joebmz98/MC8P-Mini-MIDI-Controller/images/photos/20260501_085314.jpg

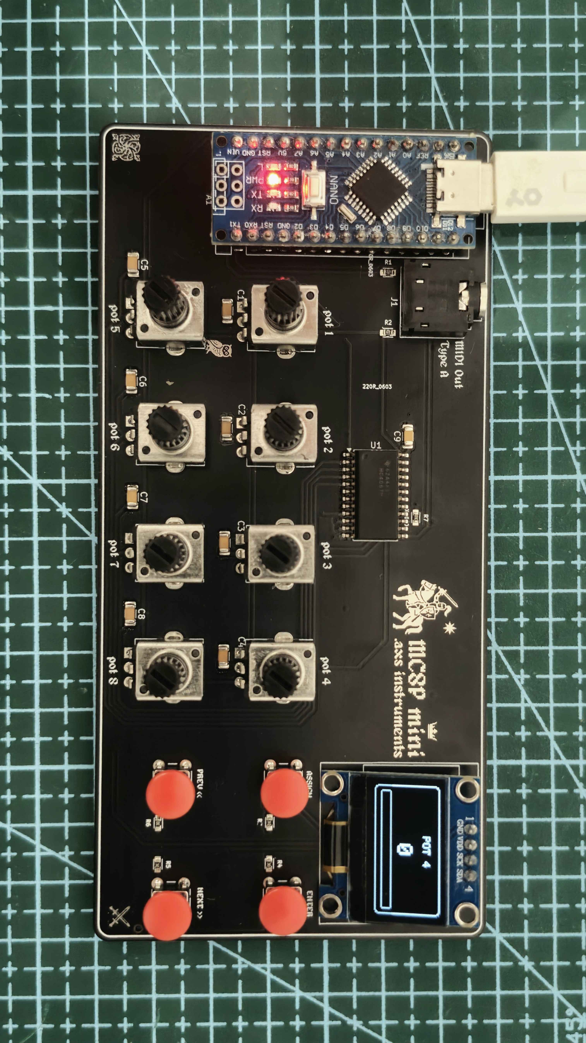
images/photos/20260501_085314.jpg
