joebmz98/MC8P-Mini-MIDI-Controller/images/photos/P1155457.jpg

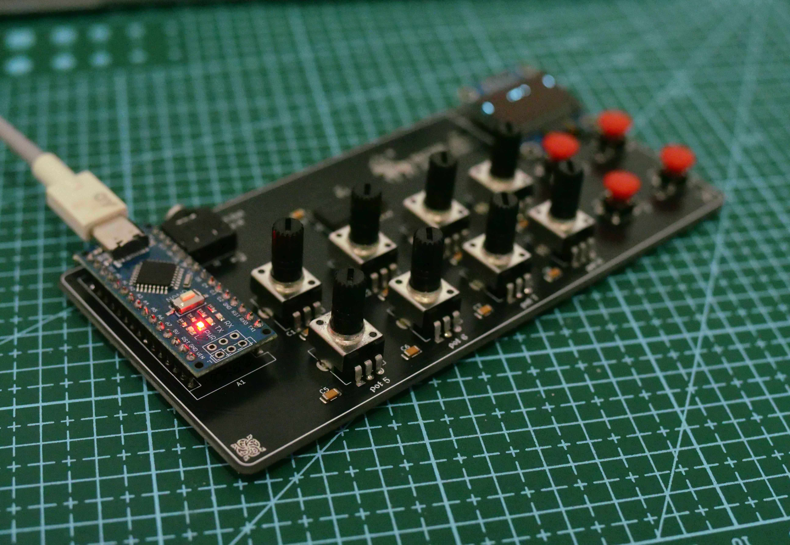
images/photos/P1155457.jpg
