joebmz98/MC8P-Mini-MIDI-Controller/images/photos/P1155459.jpg

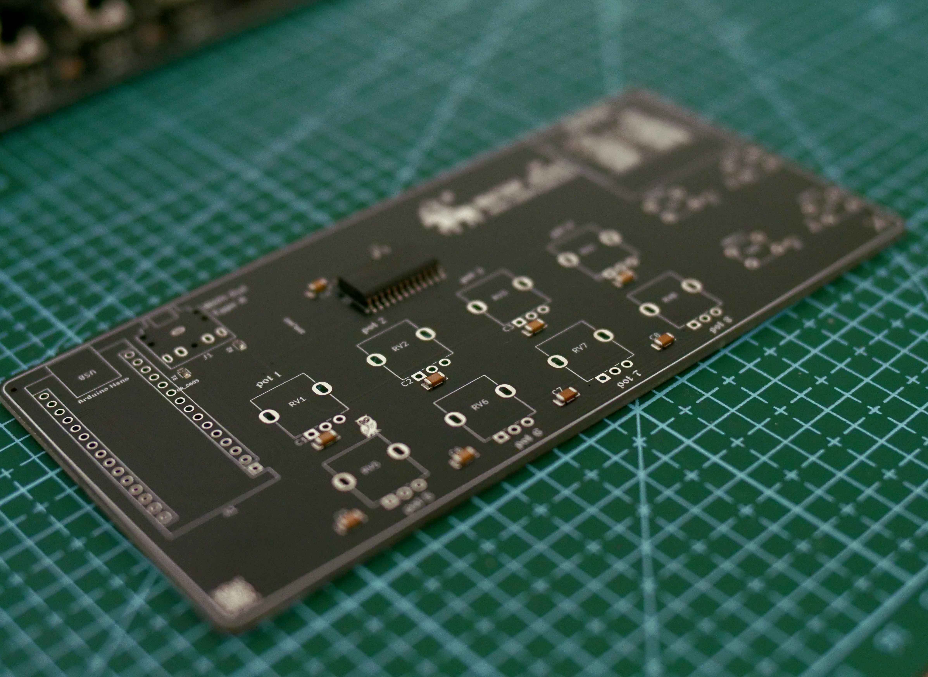
images/photos/P1155459.jpg
