joebmz98/MC8P-Mini-MIDI-Controller/images/photos/P1155460.jpg

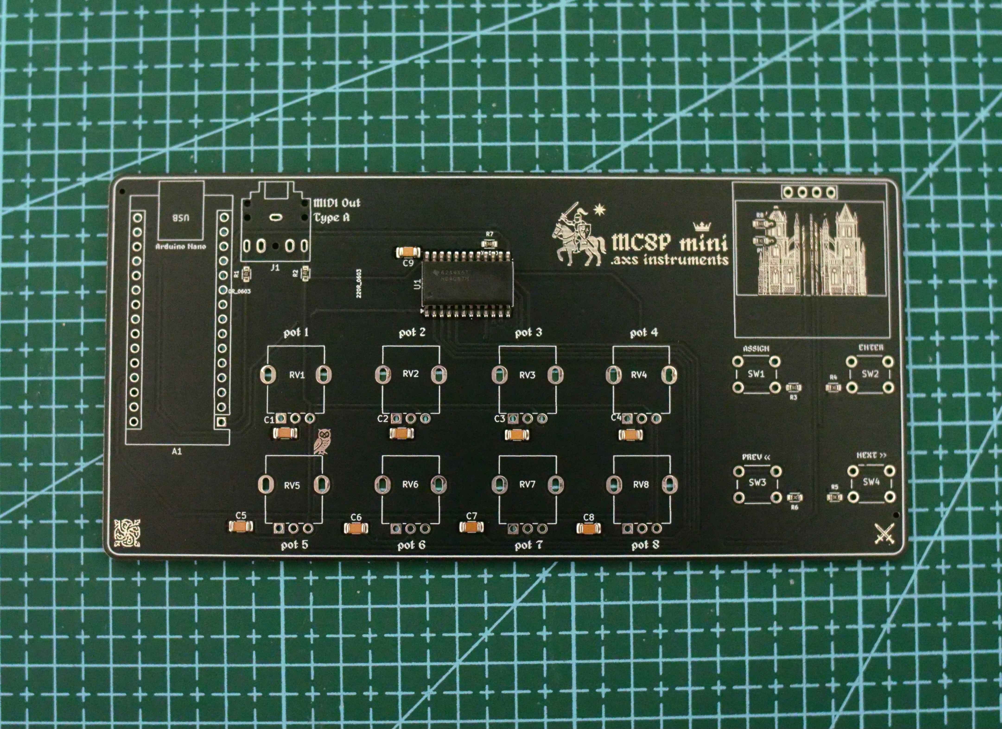
images/photos/P1155460.jpg
