joebmz98/MC8P-Mini-MIDI-Controller/images/photos/P1155462.jpg

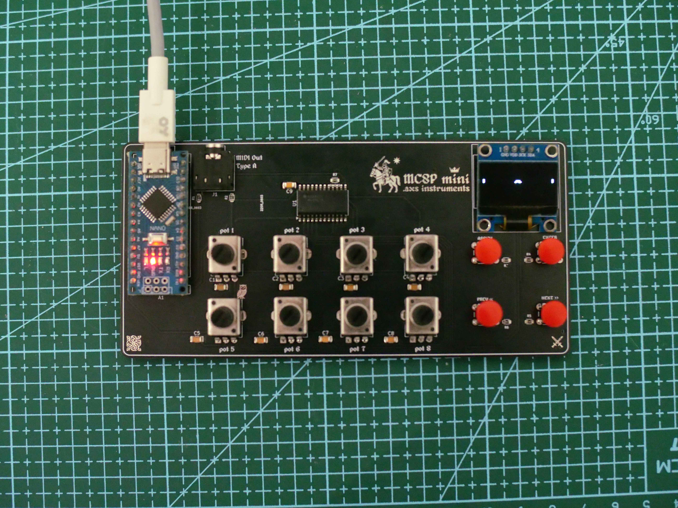
images/photos/P1155462.jpg
